Raziz1/Solar_PCB/Simulations/LT3652_Simulation.asc

C1: cap; .2m
C2: cap; 1µ
C3: cap; 10µ
C4: cap; 10µ
C5: cap; 1µ
D1: schottky; 1N5817
D2: schottky; MBRS340
D3: LED
D4: LED
D5: schottky; 1N5817
I1: current; 0.018
L1: ind; 24µ; Ipk=3.25 Rser=39.5m
R1: res; 0.25
R2: res; 412k
R3: res; 330k
R4: res; 1.1k
R5: res; 1.1k
R6: res; 68k
R7: res; 270k
R8: res; 100k
U1: LT3652
V1: voltage; 12; Rser=34.2
Named nets: 0, IN, OUT
.tran 150m startup
Solar Panel Input
12V 4.2W 350mA
Decoupling Cap
Max Charge Current 0.4A
Arduino Load
Decoupling Cap
Decoupling Cap
.ic V(OUT)=6.5
